konachan700/Mew/promo/hardware/1538132810944.JPEG

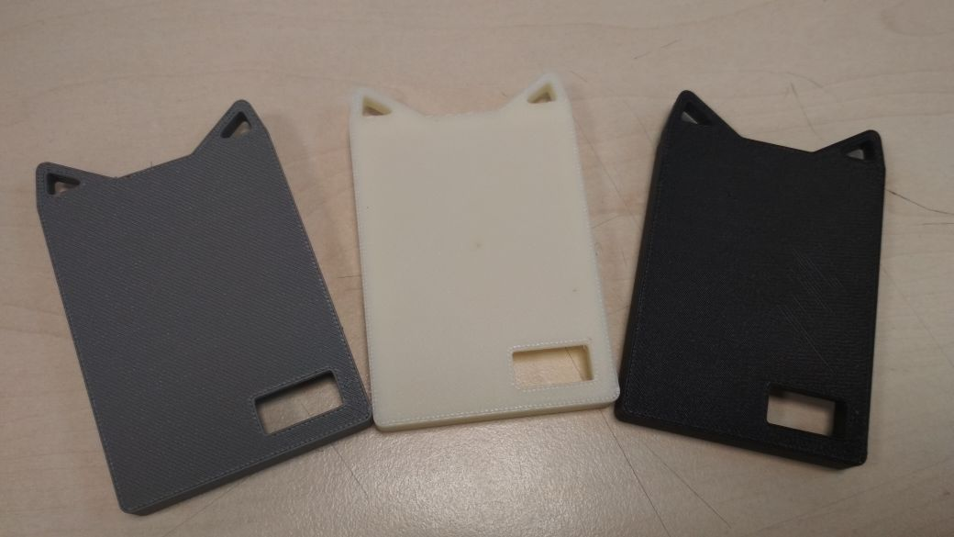
promo/hardware/1538132810944.JPEG
