konachan700/Mew/promo/render/0001.png

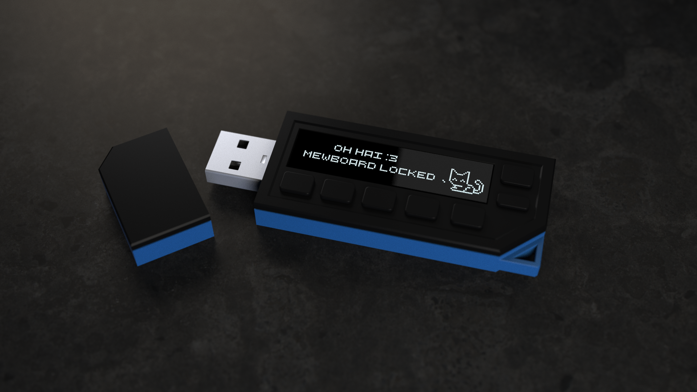
promo/render/0001.png
