konachan700/Mew/promo/render/0002.png

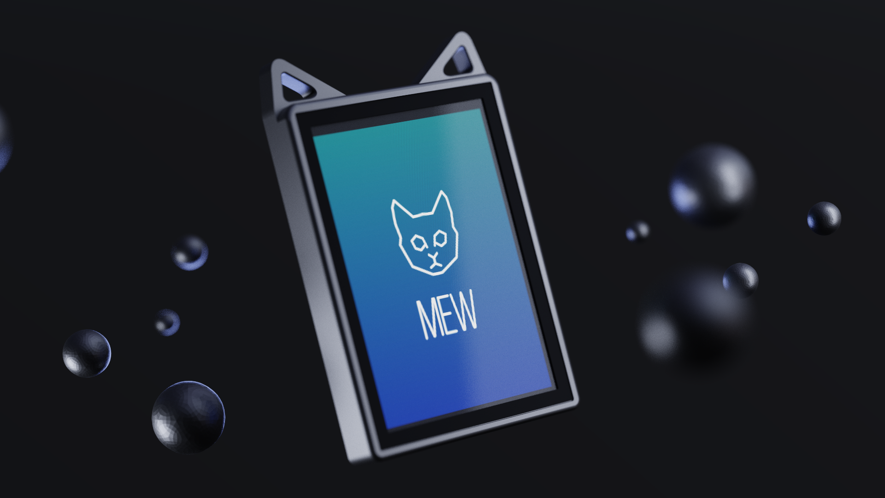
promo/render/0002.png
