konachan700/Mew/promo/render/0003.png

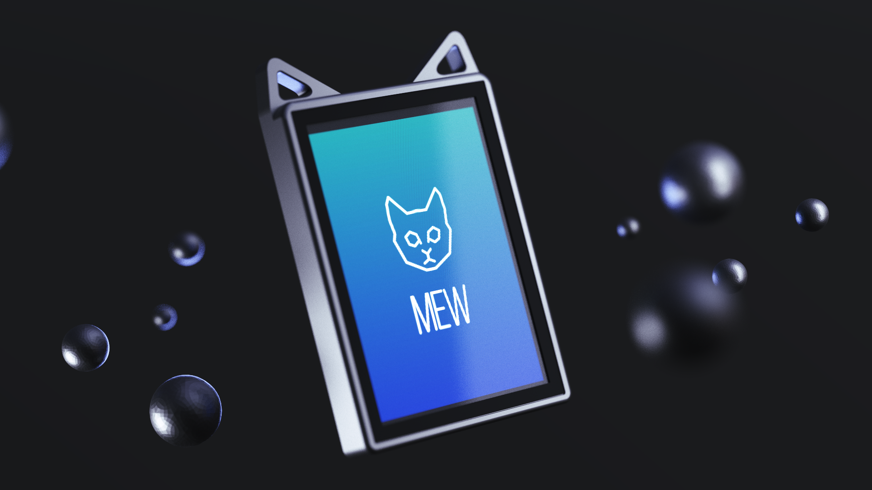
promo/render/0003.png
