konachan700/Mew/promo/render/0004.png

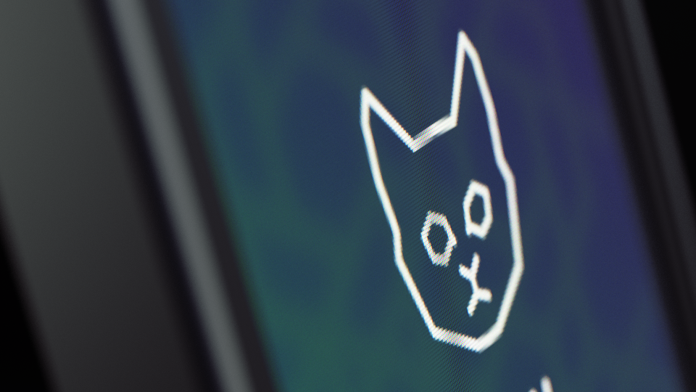
promo/render/0004.png
