konachan700/Mew/promo/render/0005.png

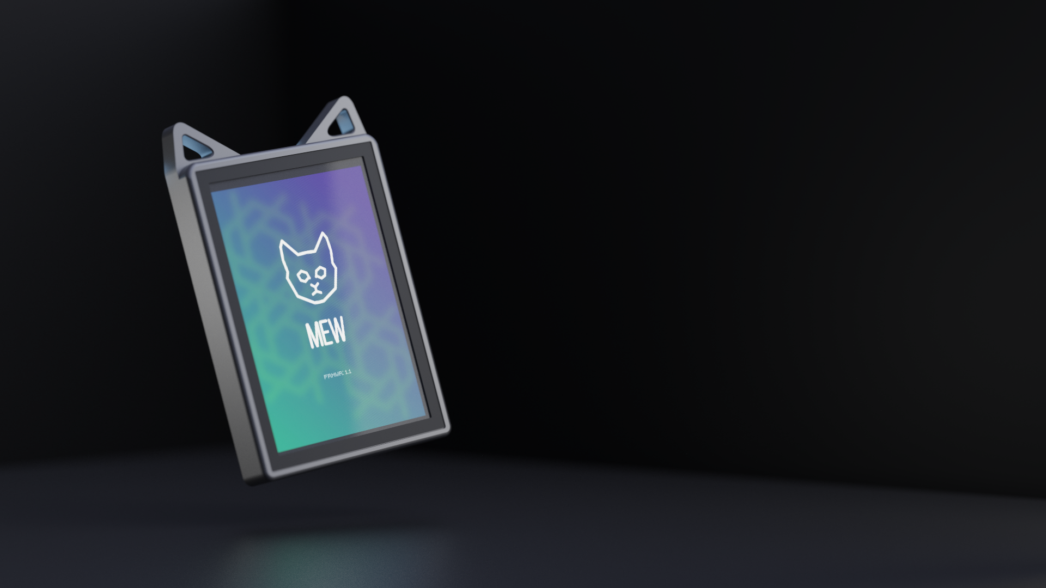
promo/render/0005.png
