konachan700/Mew/promo/render/gazdfqqvsle1zlctghrpova6sw4.png

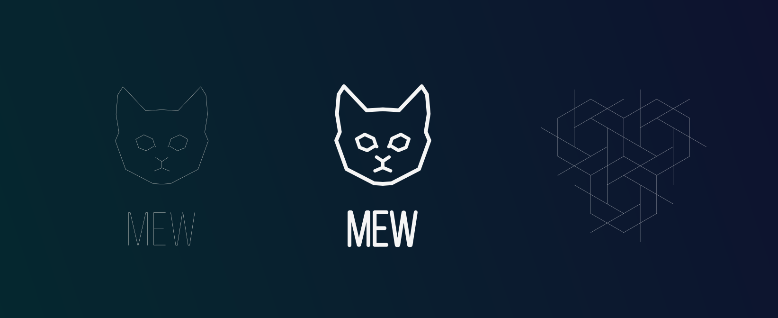
promo/render/gazdfqqvsle1zlctghrpova6sw4.png
