konachan700/Mew/firmware/drivers/display/display.h

#ifndef MEW_DISPLAY_CONFIG
#define MEW_DISPLAY_CONFIG

#include "mew.h"

#include <libopencm3/stm32/gpio.h>
#include <libopencm3/stm32/spi.h>
#include <libopencm3/stm32/dma.h>
#include <libopencm3/cm3/nvic.h>
#include <libopencm3/stm32/exti.h>

#include "lv_conf.h"
#include "lvgl/lvgl.h"

#define MEW_12BIT_SWAP(n)                   (((n & 0xFF) << 4) | (n >> 12))

#define MEW_DISPLAY_W                       240
#define MEW_DISPLAY_H                       320
#define MEW_DISPLAY_BUFFER_SIZE             (MEW_DISPLAY_W * MEW_DISPLAY_H)

#define MEW_DISPLAY_DMA                     DMA1
#define MEW_DISPLAY_DMA_HANDLE              dma1_stream4_isr
#define MEW_DISPLAY_SPI_I2SCFGR             SPI2_I2SCFGR
#define MEW_DISPLAY_DMA_STREAM              DMA_STREAM4
#define MEW_DISPLAY_DMA_CHANNEL             DMA_SxCR_CHSEL_0
#define MEW_DISPLAY_DMA_DR                  SPI2_DR
#define MEW_DISPLAY_DMA_NVIC                NVIC_DMA1_STREAM4_IRQ

#define MEW_DISPLAY_SPI                     SPI2
#define MEW_DISPLAY_SPI_GPIO_PINS           GPIO15 | GPIO13 | GPIO14
#define MEW_DISPLAY_SPI_GPIO_PORT           GPIOB
#define MEW_DISPLAY_SPI_GPIO_AF_NUMBER      GPIO_AF5

#define MEW_DISPLAY_BL_PIN                  GPIO11
#define MEW_DISPLAY_BL_PORT                 GPIOC

#define MEW_DISPLAY_RESET_PIN               GPIO12
#define MEW_DISPLAY_RESET_PORT              GPIOB

#define MEW_DISPLAY_DC_PIN                  GPIO11
#define MEW_DISPLAY_DC_PORT                 GPIOB

#define MEW_DISPLAY_CS_PIN                  GPIO10
#define MEW_DISPLAY_CS_PORT                 GPIOB

#define MEW_TSC2007_IRQ_PIN                 GPIO2
#define MEW_TSC2007_IRQ_PORT                GPIOC
#define MEW_TSC2007_IRQ_ISR                 exti2_isr
#define MEW_TSC2007_IRQ_EXTI                EXTI2
#define MEW_TSC2007_IRQ_NVIC                NVIC_EXTI2_IRQ

#define MEW_TSC2007_MEASURE_TEMP0           (0x0 << 4)
#define MEW_TSC2007_MEASURE_AUX             (0x2 << 4)
#define MEW_TSC2007_MEASURE_TEMP1           (0x4 << 4)
#define MEW_TSC2007_ACTIVATE_XN             (0x8 << 4)
#define MEW_TSC2007_ACTIVATE_YN             (0x9 << 4)
#define MEW_TSC2007_ACTIVATE_YP_XN          (0xa << 4)
#define MEW_TSC2007_SETUP                   (0xb << 4)
#define MEW_TSC2007_MEASURE_X               (0xc << 4)
#define MEW_TSC2007_MEASURE_Y               (0xd << 4)
#define MEW_TSC2007_MEASURE_Z1              (0xe << 4)
#define MEW_TSC2007_MEASURE_Z2              (0xf << 4)

#define MEW_TSC2007_POWER_OFF_IRQ_EN        (0x0 << 2)
#define MEW_TSC2007_ADC_ON_IRQ_DIS0         (0x1 << 2)
#define MEW_TSC2007_ADC_OFF_IRQ_EN          (0x2 << 2)
#define MEW_TSC2007_ADC_ON_IRQ_DIS1         (0x3 << 2)

#define MEW_TSC2007_12BIT                   (0x0 << 1)
#define MEW_TSC2007_8BIT                    (0x1 << 1)

#define	MEW_TSC2007_MAX_12BIT               ((1 << 12) - 1)

#define MEW_TSC2007_ADC_ON_12BIT	(MEW_TSC2007_12BIT | MEW_TSC2007_ADC_ON_IRQ_DIS0)

#define MEW_TSC2007_READ_Y		(MEW_TSC2007_ADC_ON_12BIT  | MEW_TSC2007_MEASURE_Y)
#define MEW_TSC2007_READ_Z1		(MEW_TSC2007_ADC_ON_12BIT  | MEW_TSC2007_MEASURE_Z1)
#define MEW_TSC2007_READ_Z2		(MEW_TSC2007_ADC_ON_12BIT  | MEW_TSC2007_MEASURE_Z2)
#define MEW_TSC2007_READ_X		(MEW_TSC2007_ADC_ON_12BIT  | MEW_TSC2007_MEASURE_X)
#define MEW_TSC2007_PWRDOWN		(MEW_TSC2007_12BIT | MEW_TSC2007_POWER_OFF_IRQ_EN)

unsigned int mew_display_init(void);
unsigned int mew_touchscreen_init(void);

void mew_display_flush(lv_disp_drv_t * disp, const lv_area_t * area, lv_color_t * color_p);
void mew_display_flush_sync(lv_disp_drv_t * disp, const lv_area_t * area, lv_color_t * color_p);
void mew_display_flush_sync_ext(int32_t x1, int32_t y1, int32_t x2, int32_t y2, lv_color_t * color_p);

#endif
