konachan700/Mew/firmware/drivers/i2c/i2c.c

#include "i2c.h"
#include "debug.h"

unsigned int mew_i2c_init(void) {
    gpio_mode_setup(MEW_I2C_TS_SCL_PORT, GPIO_MODE_AF, GPIO_PUPD_NONE, MEW_I2C_TS_SCL_PIN);
    gpio_set_output_options(MEW_I2C_TS_SCL_PORT, GPIO_OTYPE_OD, GPIO_OSPEED_100MHZ, MEW_I2C_TS_SCL_PIN);
    gpio_set_af(MEW_I2C_TS_SCL_PORT, MEW_I2C_TS_SCL_AF, MEW_I2C_TS_SCL_PIN);
    
    gpio_mode_setup(MEW_I2C_TS_SDA_PORT, GPIO_MODE_AF, GPIO_PUPD_NONE, MEW_I2C_TS_SDA_PIN);
    gpio_set_output_options(MEW_I2C_TS_SDA_PORT, GPIO_OTYPE_OD, GPIO_OSPEED_100MHZ, MEW_I2C_TS_SDA_PIN);
    gpio_set_af(MEW_I2C_TS_SDA_PORT, MEW_I2C_TS_SDA_AF, MEW_I2C_TS_SDA_PIN);

    i2c_reset(MEW_I2C_TS_I2C);
    i2c_set_standard_mode(MEW_I2C_TS_I2C);
    i2c_set_clock_frequency(MEW_I2C_TS_I2C, I2C_CR2_FREQ_2MHZ);
    i2c_set_ccr(MEW_I2C_TS_I2C, 20);
    i2c_peripheral_enable(MEW_I2C_TS_I2C);
    
    return 0;
}

uint8_t mew_i2c_read_block_ts2007(uint8_t dev_addr, uint8_t cmd, uint8_t* data, uint8_t size) {
    uint8_t i;
    
    i2c_send_start(MEW_I2C_TS_I2C);
    while ((I2C_SR1(MEW_I2C_TS_I2C) & I2C_SR1_SB) == 0);

    i2c_send_7bit_address(MEW_I2C_TS_I2C, dev_addr, I2C_WRITE);
    while ((I2C_SR1(MEW_I2C_TS_I2C) & I2C_SR1_ADDR) == 0);

    if ((I2C_SR2(MEW_I2C_TS_I2C) & I2C_SR2_MSL) && (I2C_SR2(MEW_I2C_TS_I2C) & I2C_SR2_BUSY)) { 
        i2c_send_data(MEW_I2C_TS_I2C, cmd);
        while ((I2C_SR1(MEW_I2C_TS_I2C) & I2C_SR1_TxE) == 0);
        
        i2c_send_start(MEW_I2C_TS_I2C);
        while ((I2C_SR1(MEW_I2C_TS_I2C) & I2C_SR1_SB) == 0);

        i2c_send_7bit_address(MEW_I2C_TS_I2C, dev_addr, I2C_READ);
        while ((I2C_SR1(MEW_I2C_TS_I2C) & I2C_SR1_ADDR) == 0);
        
        if (I2C_SR2(MEW_I2C_TS_I2C) & I2C_SR2_BUSY) {
            switch (size) {
                case 0:
                    mew_debug_die_with_message("mew_i2c_read_block_ts2007: Bad usage");
                    break;
                case 1:
                    while ((I2C_SR1(MEW_I2C_TS_I2C) & I2C_SR1_RxNE) == 0);
                    data[0] = i2c_get_data(MEW_I2C_TS_I2C);
                    
                    break;
                case 2:
                    i2c_enable_ack(MEW_I2C_TS_I2C);
                    while ((I2C_SR1(MEW_I2C_TS_I2C) & I2C_SR1_RxNE) == 0);
                    data[0] = i2c_get_data(MEW_I2C_TS_I2C);
                    
                    i2c_disable_ack(MEW_I2C_TS_I2C);
                    while ((I2C_SR1(MEW_I2C_TS_I2C) & I2C_SR1_RxNE) == 0);
                    data[1] = i2c_get_data(MEW_I2C_TS_I2C);
                    
                    break;
                default:
                    i2c_enable_ack(MEW_I2C_TS_I2C);
                    for (i=0; i<size; i++) {
                        if ((size - i) == 2) {
                            i2c_disable_ack(MEW_I2C_TS_I2C);
                        }
                        while ((I2C_SR1(MEW_I2C_TS_I2C) & I2C_SR1_RxNE) == 0);
                        data[i] = i2c_get_data(MEW_I2C_TS_I2C);
                    }
            }

            i2c_send_stop(MEW_I2C_TS_I2C);
            return 1;
        }
    }
    return 0;
}


uint8_t mew_i2c_read(uint8_t dev_addr, uint16_t data_addr, uint8_t* data, uint8_t mode) {
    i2c_send_start(MEW_I2C_TS_I2C);
    while ((I2C_SR1(MEW_I2C_TS_I2C) & I2C_SR1_SB) == 0);

    i2c_send_7bit_address(MEW_I2C_TS_I2C, dev_addr, I2C_WRITE);
    while ((I2C_SR1(MEW_I2C_TS_I2C) & I2C_SR1_ADDR) == 0);

    if ((I2C_SR2(MEW_I2C_TS_I2C) & I2C_SR2_MSL) && (I2C_SR2(MEW_I2C_TS_I2C) & I2C_SR2_BUSY)) { 
        if (mode == MEW_I2C_MODE_16BIT) {
            i2c_send_data(MEW_I2C_TS_I2C, ((uint8_t) (data_addr >> 8)));
            while ((I2C_SR1(MEW_I2C_TS_I2C) & I2C_SR1_TxE) == 0);
        }
        i2c_send_data(MEW_I2C_TS_I2C, ((uint8_t) data_addr));
        while ((I2C_SR1(MEW_I2C_TS_I2C) & I2C_SR1_TxE) == 0);

        i2c_send_start(MEW_I2C_TS_I2C);
        while ((I2C_SR1(MEW_I2C_TS_I2C) & I2C_SR1_SB) == 0);

        i2c_send_7bit_address(MEW_I2C_TS_I2C, dev_addr, I2C_READ);
        while ((I2C_SR1(MEW_I2C_TS_I2C) & I2C_SR1_ADDR) == 0);
        

        if (I2C_SR2(MEW_I2C_TS_I2C) & I2C_SR2_BUSY) {
            while ((I2C_SR1(MEW_I2C_TS_I2C) & I2C_SR1_RxNE) == 0);
            
            *data = i2c_get_data(MEW_I2C_TS_I2C);
            
            i2c_send_stop(MEW_I2C_TS_I2C);
            return 1;
        }
    }
    return 0;
}

uint8_t mew_i2c_write(uint8_t dev_addr, uint16_t data_addr, uint8_t data, uint8_t mode) {
    i2c_send_start(MEW_I2C_TS_I2C);
    while ((I2C_SR1(MEW_I2C_TS_I2C) & I2C_SR1_SB) == 0);

    i2c_send_7bit_address(MEW_I2C_TS_I2C, dev_addr, I2C_WRITE);
    while ((I2C_SR1(MEW_I2C_TS_I2C) & I2C_SR1_ADDR) == 0);

    if ((I2C_SR2(MEW_I2C_TS_I2C) & I2C_SR2_MSL) && (I2C_SR2(MEW_I2C_TS_I2C) & I2C_SR2_BUSY)) { 
        if (mode == MEW_I2C_MODE_16BIT) {
            i2c_send_data(MEW_I2C_TS_I2C, ((uint8_t)(data_addr >> 8)));
            while ((I2C_SR1(MEW_I2C_TS_I2C) & I2C_SR1_TxE) == 0);
        }

        i2c_send_data(MEW_I2C_TS_I2C, ((uint8_t) data_addr));
        while ((I2C_SR1(MEW_I2C_TS_I2C) & I2C_SR1_TxE) == 0);

        if (mode == MEW_I2C_MODE_8BIT || mode == MEW_I2C_MODE_16BIT) {
            i2c_send_data(MEW_I2C_TS_I2C, data);
            while ((I2C_SR1(MEW_I2C_TS_I2C) & I2C_SR1_TxE) == 0);
        }

        i2c_send_stop(MEW_I2C_TS_I2C);
        return 1;
    }
    
    return 0;
}

unsigned int mew_i2c_eeprom_test(void) {
#ifdef __MEW_FACTORY_TESTS__
	mew_debug_print("mew_i2c_eeprom_test...");
	uint16_t i;

	uint8_t data_in[MEW_I2C_EEPROM_PAGE_SIZE];
	for (i=0; i<MEW_I2C_EEPROM_PAGE_SIZE; i++) data_in[i] = (uint8_t) i;
	mew_i2c_eeprom_write(3, data_in);

	uint8_t data_out[MEW_I2C_EEPROM_PAGE_SIZE];
	mew_i2c_eeprom_read(3, data_out);

	if (memcmp(data_in, data_out, MEW_I2C_EEPROM_PAGE_SIZE) == 0) {
		mew_debug_print("mew_i2c_eeprom_test: ok");
	} else {
		mew_debug_print("mew_i2c_eeprom_test: fail");
		mew_debug_print("Readed:");
		mew_debug_print_hex((const char *)data_out, MEW_I2C_EEPROM_PAGE_SIZE);
		mew_debug_print("Origin:");
		mew_debug_print_hex((const char *)data_in, MEW_I2C_EEPROM_PAGE_SIZE);
		return 1;
	}
#endif
	return 0;
}

uint8_t mew_i2c_eeprom_write(uint8_t segment_addr, uint8_t* data) {
    while ((I2C_SR2(MEW_I2C_TS_I2C) & I2C_SR2_BUSY)) {}
	i2c_send_start(MEW_I2C_TS_I2C);

	while (!((I2C_SR1(MEW_I2C_TS_I2C) & I2C_SR1_SB)& (I2C_SR2(MEW_I2C_TS_I2C) & (I2C_SR2_MSL | I2C_SR2_BUSY))));
	i2c_send_7bit_address(MEW_I2C_TS_I2C, (MEW_I2C_EEPROM_ADDR | segment_addr), I2C_WRITE);

	while (!(I2C_SR1(MEW_I2C_TS_I2C) & I2C_SR1_ADDR));
	(void)I2C_SR2(MEW_I2C_TS_I2C);

	i2c_send_data(MEW_I2C_TS_I2C, 0x00);
	while (!(I2C_SR1(MEW_I2C_TS_I2C) & (I2C_SR1_BTF)));

	for (size_t i = 0; i < MEW_I2C_EEPROM_PAGE_SIZE; i++) {
		 i2c_send_data(MEW_I2C_TS_I2C, data[i]);
		 while (!(I2C_SR1(MEW_I2C_TS_I2C) & (I2C_SR1_BTF)));
	}

	i2c_send_stop(MEW_I2C_TS_I2C);
	return 0;
}

uint8_t mew_i2c_eeprom_read(uint8_t segment_addr, uint8_t* data) {
	uint8_t* data_to = {0x00};
	i2c_transfer7(MEW_I2C_TS_I2C, (MEW_I2C_EEPROM_ADDR | segment_addr), data_to, 1, data, MEW_I2C_EEPROM_PAGE_SIZE);
	return 0;
}
