konachan700/Mew/firmware/drivers/i2c/i2c.h

#ifndef MEW_I2C_H
#define MEW_I2C_H

#include "mew.h"

#include <stdio.h>
#include <string.h>
#include <stdlib.h>

#include <libopencm3/stm32/i2c.h>
#include <libopencm3/stm32/gpio.h>
#include <libopencm3/cm3/nvic.h>
#include <libopencm3/cm3/cortex.h>

#define MEW_I2C_TS_I2C                  I2C3
#define MEW_I2C_TS_NVIC                 NVIC_I2C3_EV_IRQ
#define MEW_I2C_TS_ISR                  i2c1_ev_isr

#define MEW_I2C_TS_SCL_PORT             GPIOA
#define MEW_I2C_TS_SCL_PIN              GPIO8
#define MEW_I2C_TS_SCL_AF               GPIO_AF4

#define MEW_I2C_TS_SDA_PORT             GPIOC
#define MEW_I2C_TS_SDA_PIN              GPIO9
#define MEW_I2C_TS_SDA_AF               GPIO_AF4

#define MEW_I2C_MODE_0BIT               2
#define MEW_I2C_MODE_8BIT               0
#define MEW_I2C_MODE_16BIT              1

#define MEW_I2C_EEPROM_PAGE_SIZE		(2048 / 8)
#define MEW_I2C_EEPROM_ADDR				(0x50)

unsigned int mew_i2c_init(void);

uint8_t mew_i2c_read(uint8_t dev_addr, uint16_t data_addr, uint8_t* data, uint8_t mode);
uint8_t mew_i2c_write(uint8_t dev_addr, uint16_t data_addr, uint8_t data, uint8_t mode);

uint8_t mew_i2c_read_block_ts2007(uint8_t dev_addr, uint8_t cmd, uint8_t* data, uint8_t size);

uint8_t mew_i2c_eeprom_write(uint8_t segment_addr, uint8_t* data);
uint8_t mew_i2c_eeprom_read(uint8_t segment_addr, uint8_t* data);
unsigned int mew_i2c_eeprom_test(void) ;

#endif /* I2C_H */
