konachan700/Mew/firmware/debug.h

#ifndef MEW_DEBUG_H
#define MEW_DEBUG_H

#include "drivers/duart/duart.h"

#include <stdio.h>

void mew_debug_print(const char* message);
void mew_debug_print_hex(const char* message, unsigned int len);
void mew_debug_print_hex_ex(const char* text, const char* blob, unsigned int len);

void mew_debug_die(void);
void mew_debug_die_with_message(const char* message);

#endif /* DEBUG_H */
